particle-iot/electron/docs/images/electron-blockdiagram.png

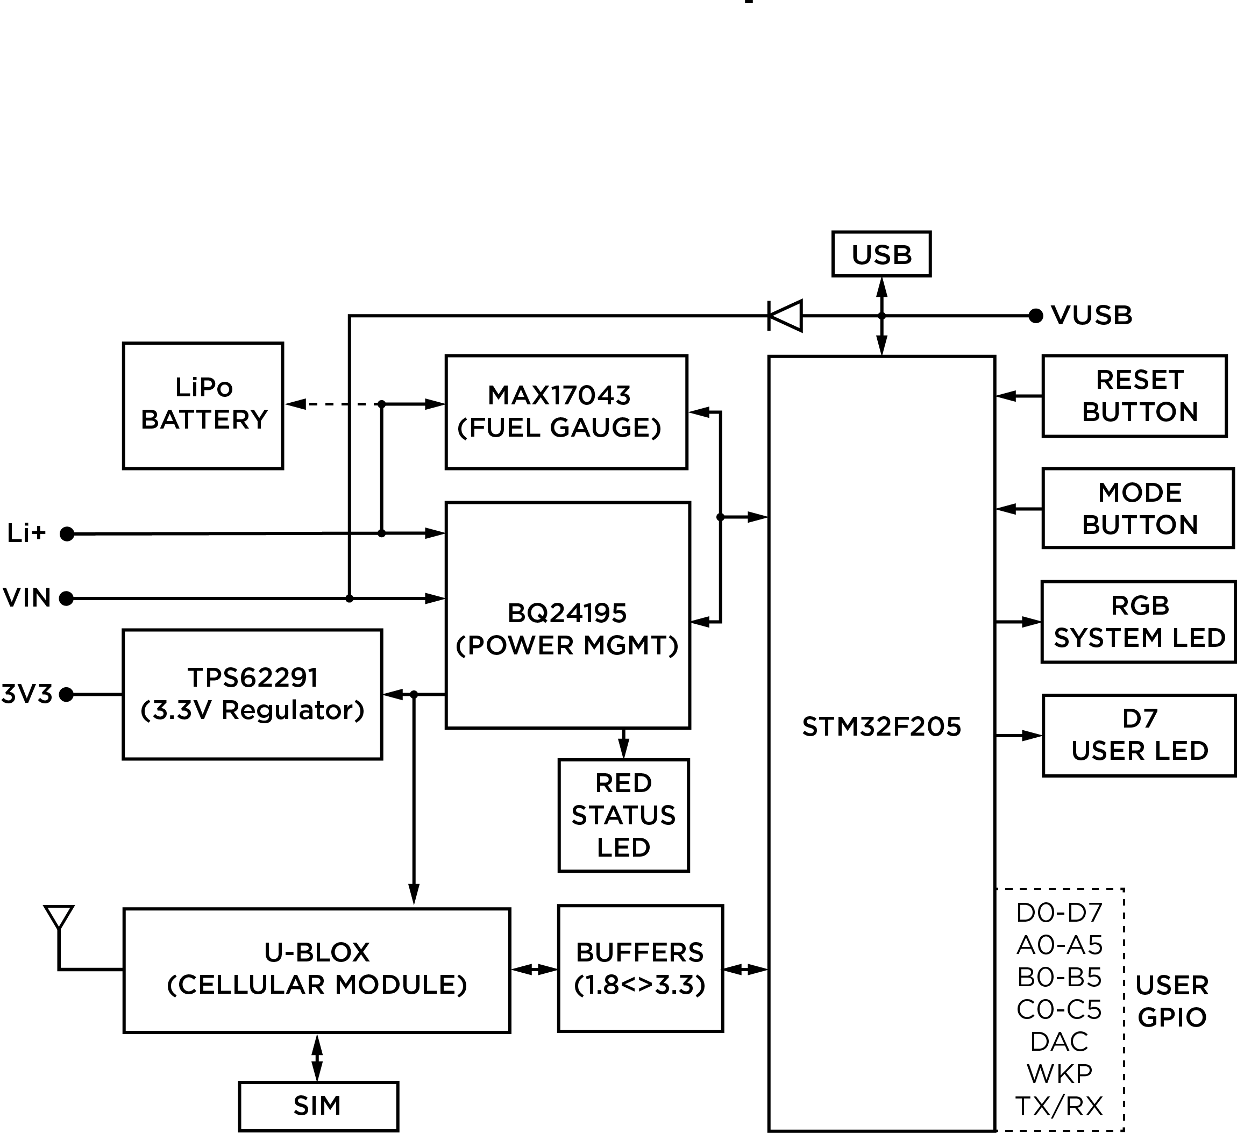
docs/images/electron-blockdiagram.png
