particle-iot/electron/mfg-docs/50ohm_calculations.png

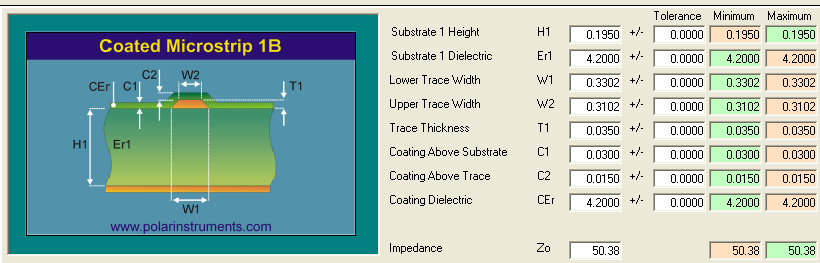
mfg-docs/50ohm_calculations.png
