particle-iot/electron/mfg-docs/layer_stackup.png

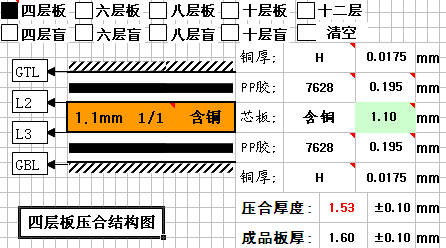
mfg-docs/layer_stackup.png
